yohanesstef/CAPSTONE/full-bridge-inverter/hb9500-barrier-teminal-block-1.snapshot.2/hb-9500-2p.jpg

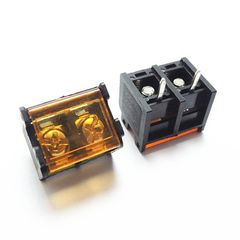
full-bridge-inverter/hb9500-barrier-teminal-block-1.snapshot.2/hb-9500-2p.jpg
