yohanesstef/CAPSTONE/full-bridge-inverter/display-oled128x32-1.snapshot.4/display2.png

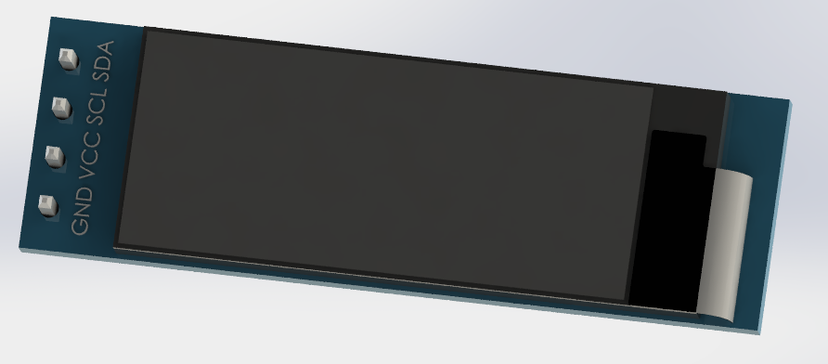
full-bridge-inverter/display-oled128x32-1.snapshot.4/display2.png
