yohanesstef/CAPSTONE/full-bridge-inverter/display-oled128x32-1.snapshot.4/display.png

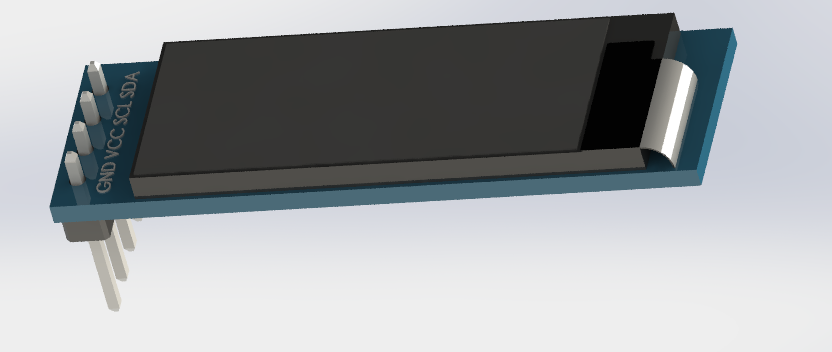
full-bridge-inverter/display-oled128x32-1.snapshot.4/display.png
