yohanesstef/CAPSTONE/full-bridge-inverter/rotary-encoder-ky-040-2.snapshot.2/Screen Shot 2022-12-16 at 3.19.57 PM.png

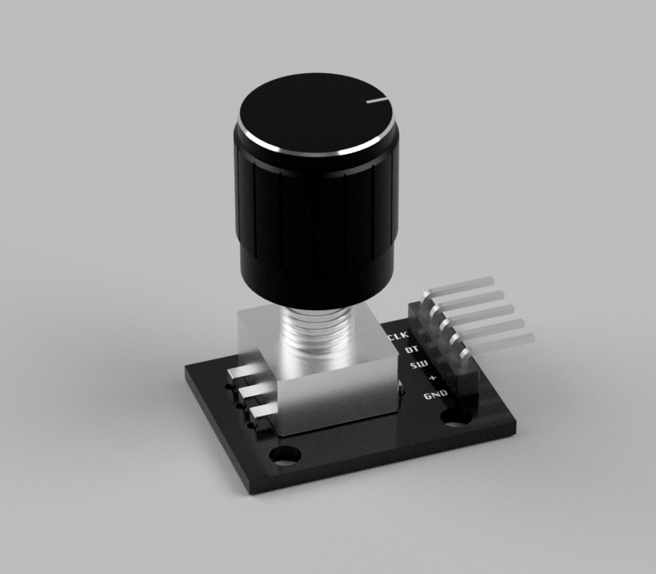
full-bridge-inverter/rotary-encoder-ky-040-2.snapshot.2/Screen Shot 2022-12-16 at 3.19.57 PM.png
