yohanesstef/CAPSTONE/full-bridge-inverter/rotary encoder step files/Step Files/rotary encoder_chesr_2013.stp

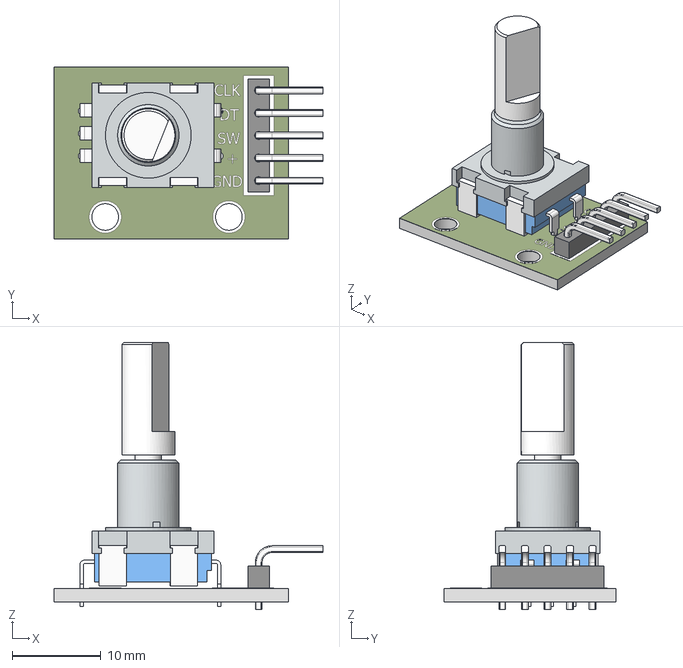
[picture p25: CAD file, 2024-08-02]
full-bridge-inverter/rotary encoder step files/Step Files/rotary encoder_chesr_2013.stp
30.3 x 19.3 x 30.1 mm
