yohanesstef/CAPSTONE/full-bridge-inverter/ky-040-rotary-encoder-1.snapshot.1/Rotary Encoder -  ODG/sw2017 model/Rotary Encoder.SLDPRT

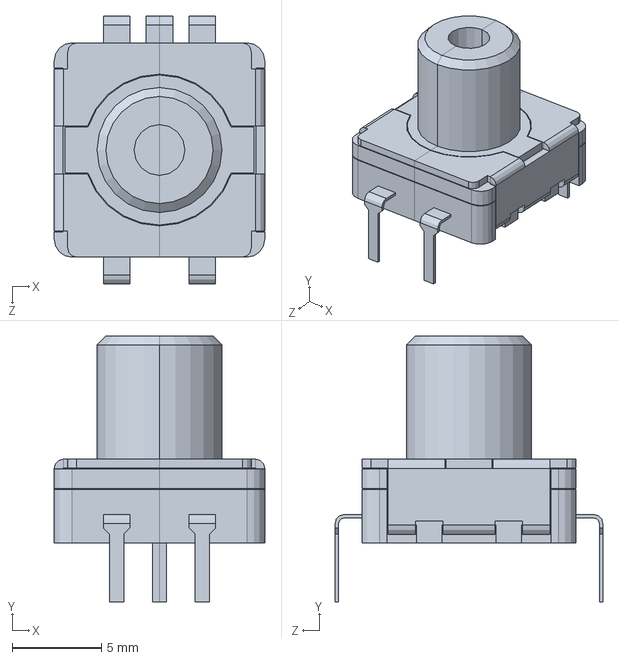
[picture p26: CAD file, 2024-08-02]
full-bridge-inverter/ky-040-rotary-encoder-1.snapshot.1/Rotary Encoder - ODG/sw2017 model/Rotary Encoder.SLDPRT
11.8 x 14.9 x 15.0 mm
