yohanesstef/CAPSTONE/full-bridge-inverter/rotary encoder step files/Step Files/90d pin_header.stp

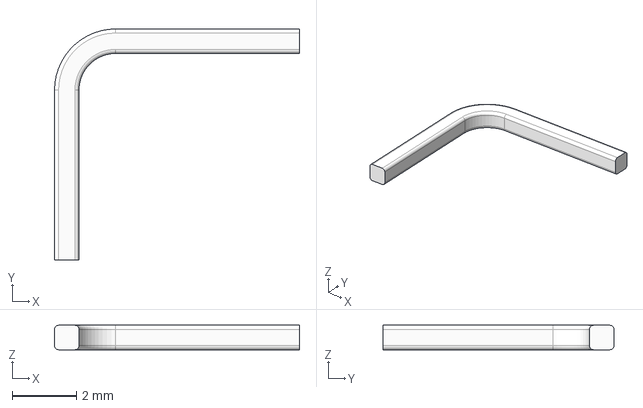
[picture p27: CAD file, 2024-08-02]
full-bridge-inverter/rotary encoder step files/Step Files/90d pin_header.stp
7.62 x 7.19 x 0.762 mm
