yohanesstef/CAPSTONE/full-bridge-inverter/ky-040-rotary-encoder-1.snapshot.1/Rotary Encoder -  ODG/sw2017 model/2.54 5PIN 90.SLDPRT

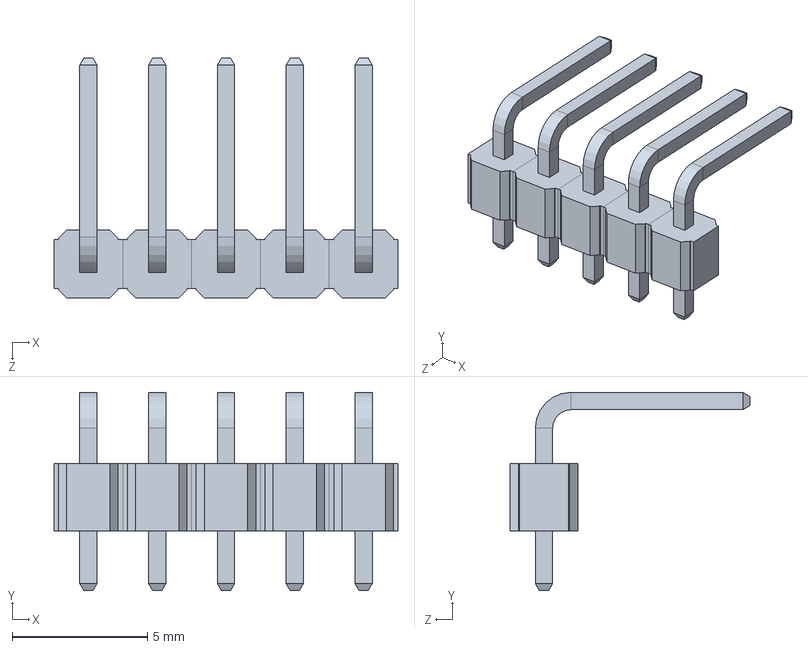
[picture p28: CAD file, 2024-08-02]
full-bridge-inverter/ky-040-rotary-encoder-1.snapshot.1/Rotary Encoder - ODG/sw2017 model/2.54 5PIN 90.SLDPRT
12.7 x 7.32 x 8.85 mm
