yohanesstef/CAPSTONE/full-bridge-inverter/rotary encoder step files/Step Files/body_2.stp

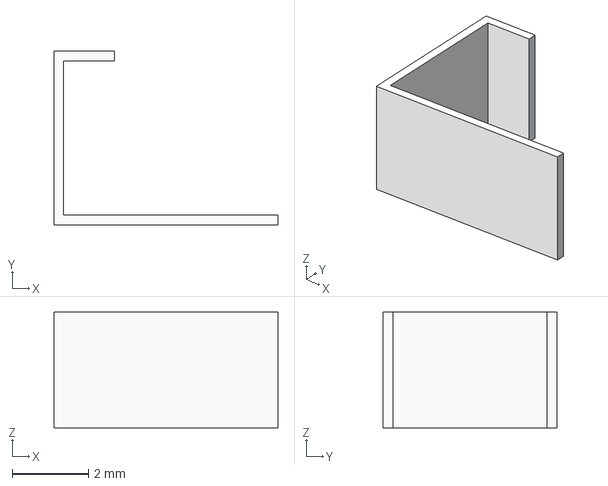
[picture p29: CAD file, 2024-08-02]
full-bridge-inverter/rotary encoder step files/Step Files/body_2.stp
5.89 x 4.57 x 3.05 mm
