yohanesstef/CAPSTONE/full-bridge-inverter/rotary encoder step files/Step Files/decal_encoder.stp

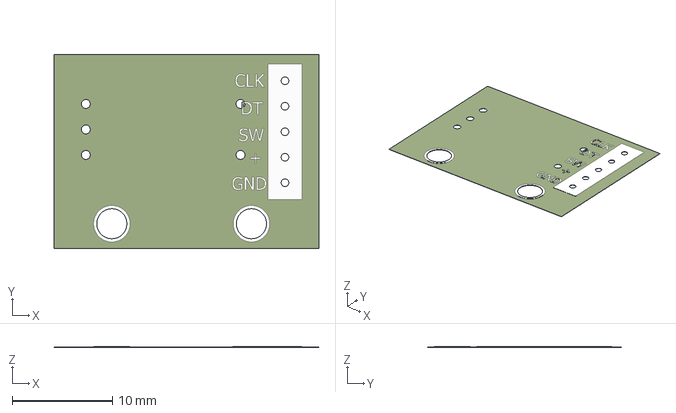
[picture p30: CAD file, 2024-08-02]
full-bridge-inverter/rotary encoder step files/Step Files/decal_encoder.stp
26.4 x 19.3 x 0.0508 mm
