yohanesstef/CAPSTONE/full-bridge-inverter/rotary encoder step files/Step Files/mtg flange.stp

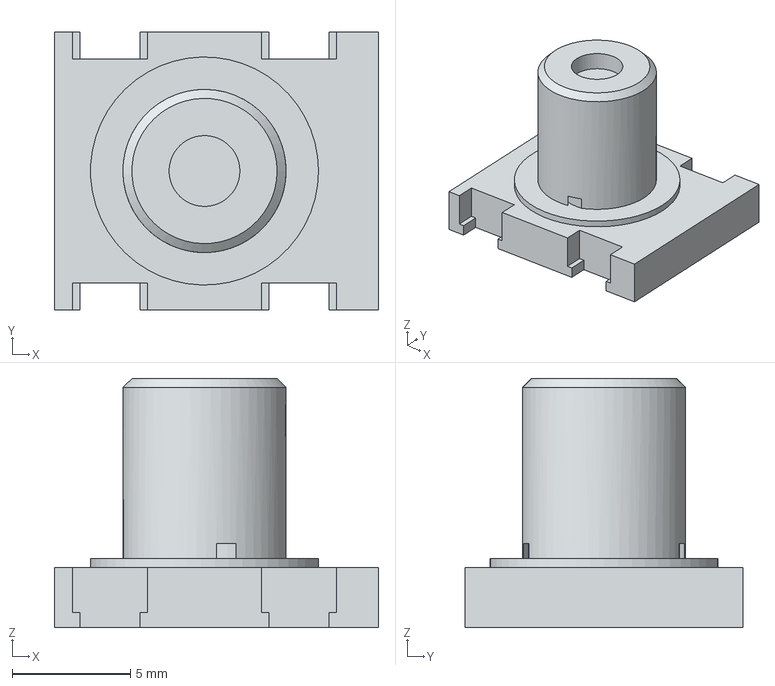
[picture p31: CAD file, 2024-08-02]
full-bridge-inverter/rotary encoder step files/Step Files/mtg flange.stp
13.7 x 11.8 x 10.5 mm
