yohanesstef/CAPSTONE/full-bridge-inverter/rotary encoder step files/Step Files/pcb.stp

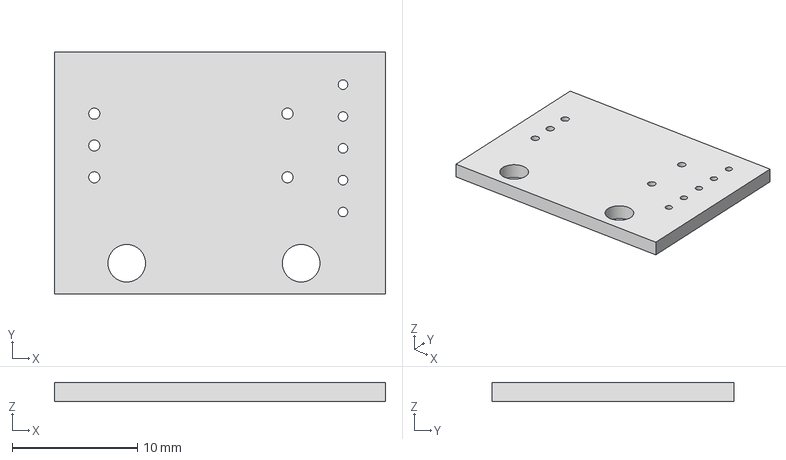
[picture p32: CAD file, 2024-08-02]
full-bridge-inverter/rotary encoder step files/Step Files/pcb.stp
26.4 x 19.3 x 1.52 mm
