yohanesstef/CAPSTONE/full-bridge-inverter/rotary encoder step files/Step Files/5 pin header.stp

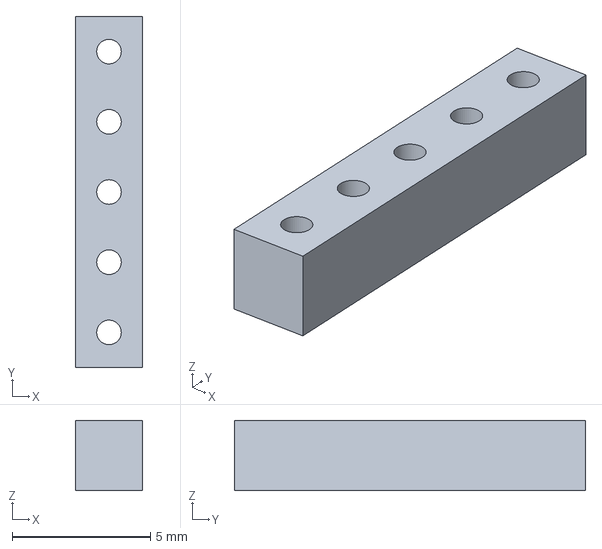
[picture p33: CAD file, 2024-08-02]
full-bridge-inverter/rotary encoder step files/Step Files/5 pin header.stp
2.41 x 12.7 x 2.54 mm
