yohanesstef/CAPSTONE/full-bridge-inverter/rotary encoder step files/Step Files/body_encoder.stp

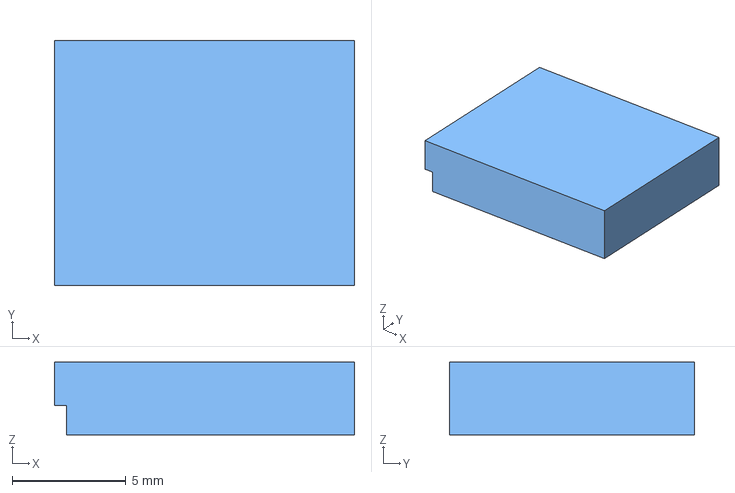
[picture p34: CAD file, 2024-08-02]
full-bridge-inverter/rotary encoder step files/Step Files/body_encoder.stp
13.2 x 10.8 x 3.20 mm
